Philip-Kiehnle/STMInverter/STMInverterPCB/Half-Bridge.kicad_sch

## KiCad design STMInverterPCB/Half-Bridge.kicad_sch (2023-06-10)

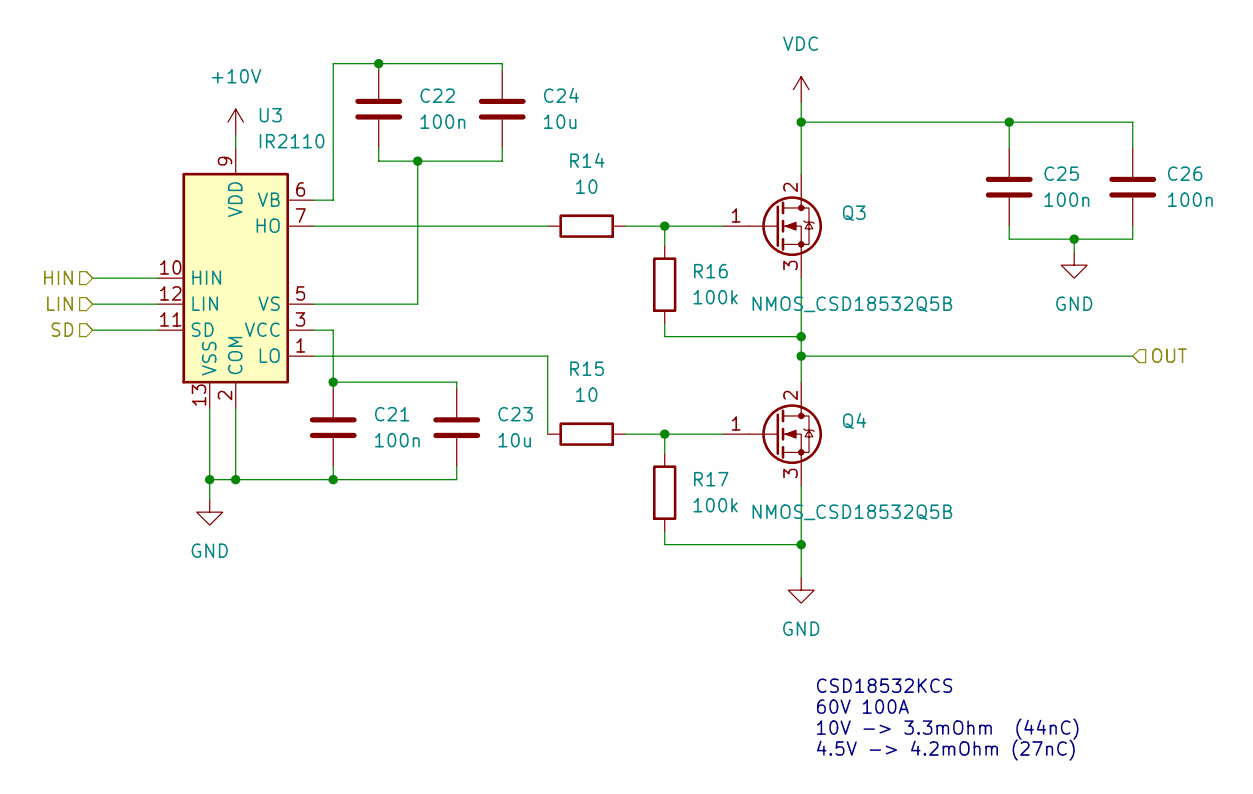
[picture p3: schematic Half-Bridge.kicad_sch]

Parts:
C21, C22, C25, C26: 100n
C23, C24: 10u
Q3, Q4: NMOS_CSD18532Q5B; TO-220-3_Horizontal_TabUp
R14, R15: 10; R_Axial_DIN0207_L6.3mm_D2.5mm_P10.16mm_Horizontal
R16, R17: 100k; R_Axial_DIN0207_L6.3mm_D2.5mm_P10.16mm_Horizontal
U3: IR2110; DIP-14_W7.62mm

Connections:
+10V: U3.9 (VDD)
GND: C21.2, C23.2, C25.2, C26.2, Q4.3 (S), R17.2, U3.2 (COM), U3.13 (VSS)
HIN: U3.10 (HIN)
LIN: U3.12 (LIN)
unnamed: C21.1, C23.1, U3.3 (VCC)
unnamed: C22.1, C24.1, U3.6 (VB)
unnamed: C22.2, C24.2, U3.5 (VS)
unnamed: Q3.1 (G), R14.2, R16.1
unnamed: Q4.1 (G), R15.2, R17.1
unnamed: R14.1, U3.7 (HO)
unnamed: R15.1, U3.1 (LO)
OUT: Q3.3 (S), Q4.2 (D), R16.2
SD: U3.11 (SD)
VDC: C25.1, C26.1, Q3.2 (D)

Notes on the sheet:
CSD18532KCS 60V 100A 10V -> 3.3mOhm (44nC) 4.5V -> 4.2mOhm (27nC)
