Philip-Kiehnle/STMInverter/STMInverterPCB/STMInverter.kicad_sch

## KiCad design STMInverterPCB/STMInverter.kicad_sch (2023-06-10)

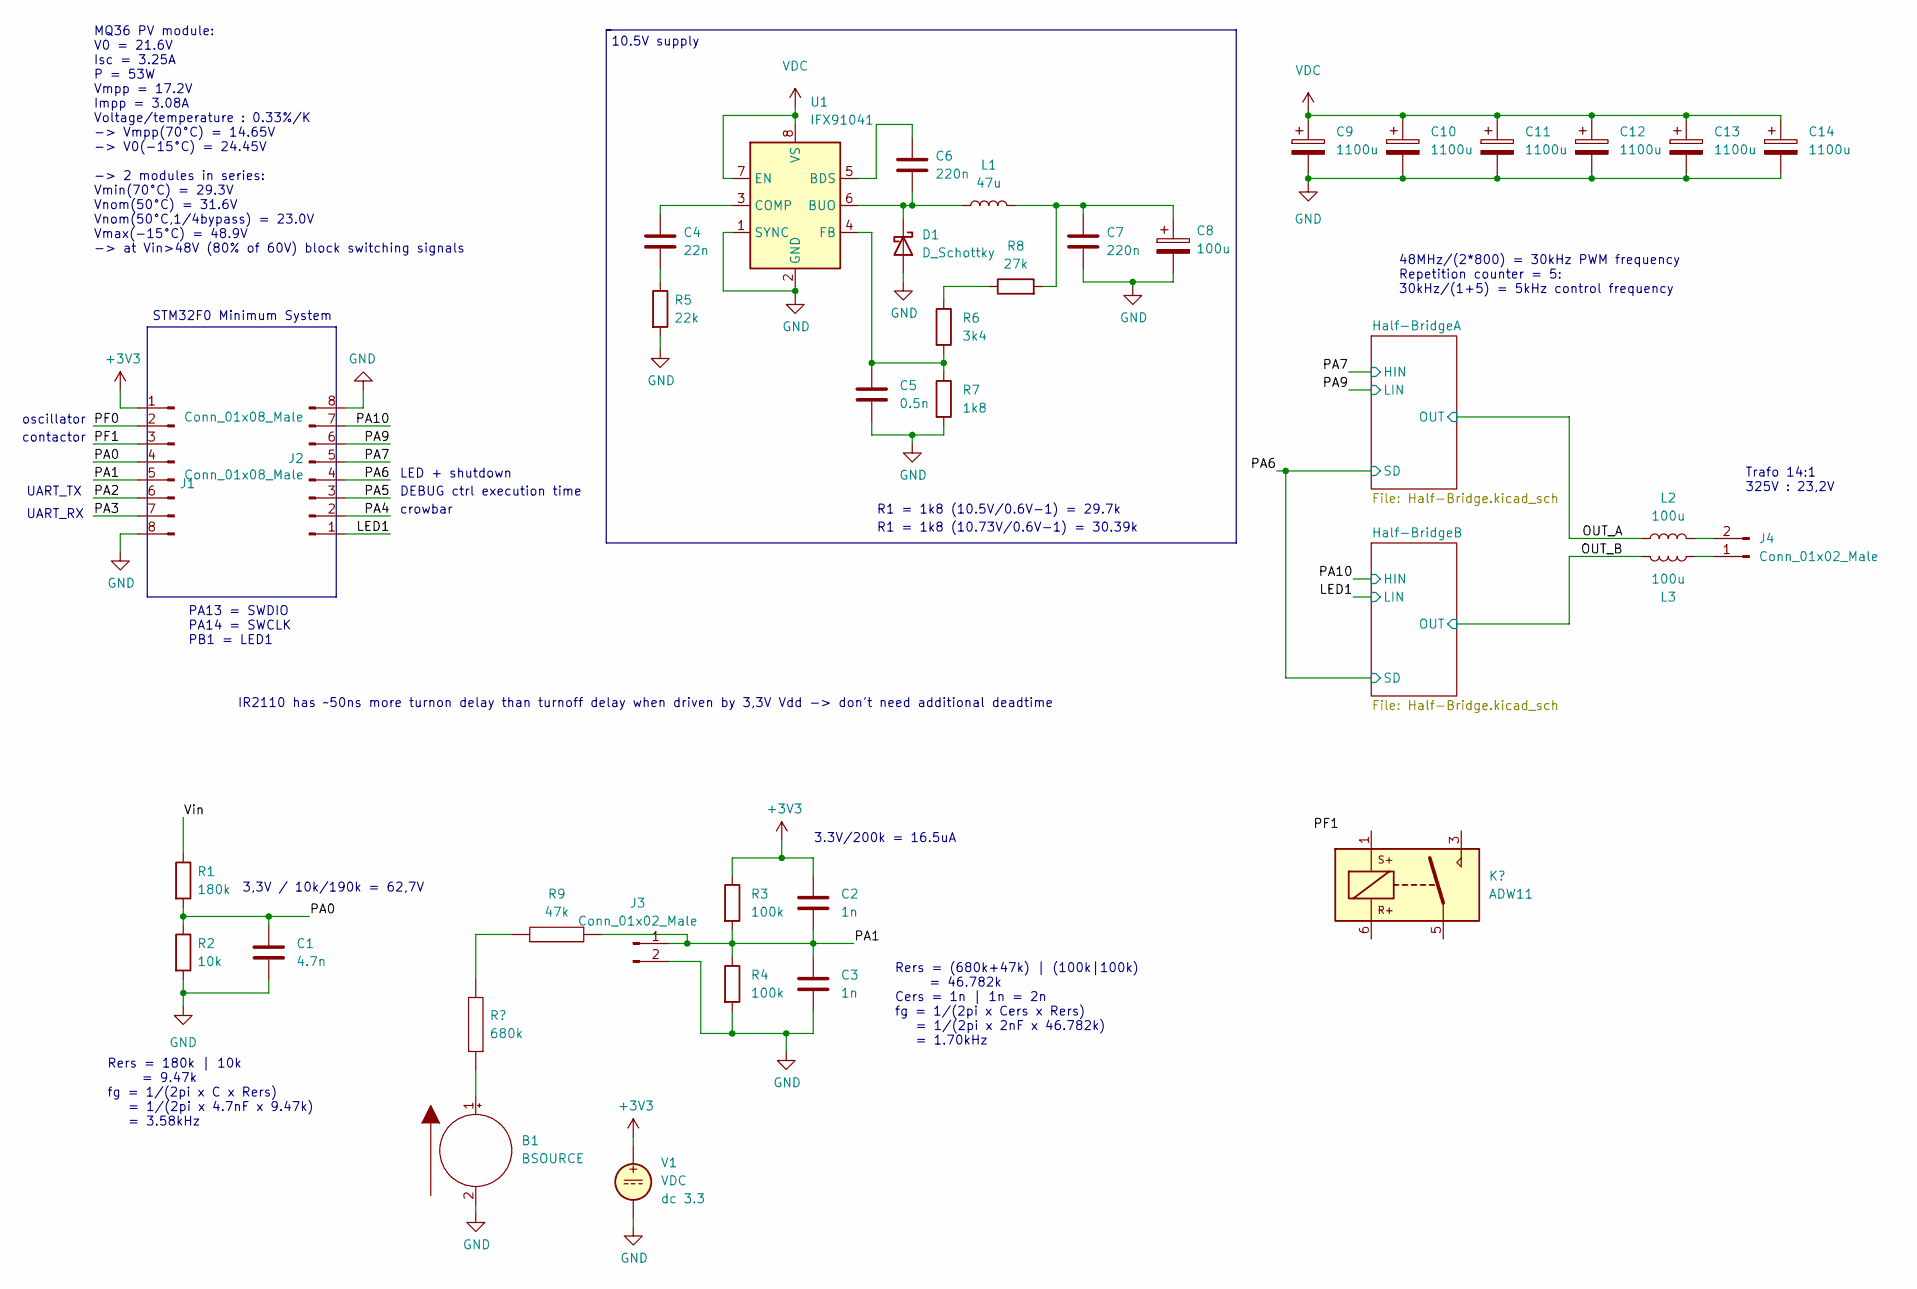
[picture p4: schematic STMInverter.kicad_sch]

Parts:
B1: BSOURCE
C1: 4.7n; C_1206_3216Metric
C2, C3: 1n
C4: 22n
C5: 0.5n
C6, C7: 220n
C8: 100u
C9, C10, C11, C12, C13, C14: 1100u
D1: D_Schottky
J1, J2: Conn_01x08_Male; PinHeader_1x08_P2.54mm_Vertical
J3, J4: Conn_01x02_Male
L1: 47u
L2, L3: 100u
R1: 180k; R_Axial_DIN0207_L6.3mm_D2.5mm_P10.16mm_Horizontal
R2: 10k; R_1206_3216Metric
R3, R4: 100k
R5: 22k
R6: 3k4
R7: 1k8
R8: 27k
R9: 47k
U1: IFX91041
V1: VDC

Connections:
+3V3: C2.1, J1.1, R3.1, V1.1
GND: B1.2 (N-), C1.2, C3.2, C5.2, C7.2, C8.2, C9.2, C10.2, C11.2, C12.2, C13.2, C14.2, D1.2 (A), J1.8, J2.8, J3.2, R2.2, R4.2, R5.2, R7.2, U1.1 (SYNC), U1.2 (GND), V1.2
LED1: J2.1
unnamed: C4.1, U1.3 (COMP)
unnamed: C4.2, R5.1
unnamed: C5.1, R6.2, R7.1, U1.4 (FB)
unnamed: C6.1, U1.5 (BDS)
unnamed: C6.2, D1.1 (K), L1.1, U1.6 (BUO)
unnamed: C7.1, C8.1, L1.2, R8.2
unnamed: J4.1, L3.1
unnamed: J4.2, L2.2
unnamed: R6.1, R8.1
OUT_A: L2.1
OUT_B: L3.2
PA0: C1.1, J1.4, R1.2, R2.1
PA1: C2.2, C3.1, J1.5, J3.1, R3.2, R4.1, R9.2
PA2: J1.6
PA3: J1.7
PA4: J2.2
PA5: J2.3
PA6: J2.4
PA7: J2.5
PA9: J2.6
PA10: J2.7
PF0: J1.2
PF1: J1.3
VDC: C9.1, C10.1, C11.1, C12.1, C13.1, C14.1, U1.7 (EN), U1.8 (VS)
Vin: R1.1

Notes on the sheet:
R1 = 1k8 (10.73V/0.6V-1) = 30.39k
PA13 = SWDIO PA14 = SWCLK PB1 = LED1
DEBUG ctrl execution time
oscillator
LED + shutdown
STM32F0 Minimum System
Trafo 14:1 325V : 23,2V
UART_RX
MQ36 PV module: V0 = 21.6V Isc = 3.25A P = 53W Vmpp = 17.2V Impp = 3.08A Voltage/temperature : 0.33%/K -> Vmpp(70°C) = 14.65V -> V0(-15°C) = 24.45V -> 2 modules in series: Vmin(70°C) = 29.3V Vnom(50°C) = 31.6V Vnom(50°C,1/4bypass) = 23.0V Vmax(-15°C) = 48.9V -> at Vin>48V (80% of 60V) block switchi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
crowbar
contactor
R1 = 1k8 (10.5V/0.6V-1) = 29.7k
Rers = 180k | 10k = 9.47k fg = 1/(2pi x C x Rers) = 1/(2pi x 4.7nF x 9.47k) = 3.58kHz
UART_TX
Rers = (680k+47k) | (100k|100k) = 46.782k Cers = 1n | 1n = 2n fg = 1/(2pi x Cers x Rers) = 1/(2pi x 2nF x 46.782k) = 1.70kHz
3.3V/200k = 16.5uA
10.5V supply
48MHz/(2*800) = 30kHz PWM frequency Repetition counter = 5: 30kHz/(1+5) = 5kHz control frequency
3,3V / 10k/190k = 62,7V
IR2110 has ~50ns more turnon delay than turnoff delay when driven by 3,3V Vdd -> don't need additional deadtime
